joshirishabh1904/BlindNav/CAD/sketches/stick_design/BlindNav_Stick_Sketch.jpeg

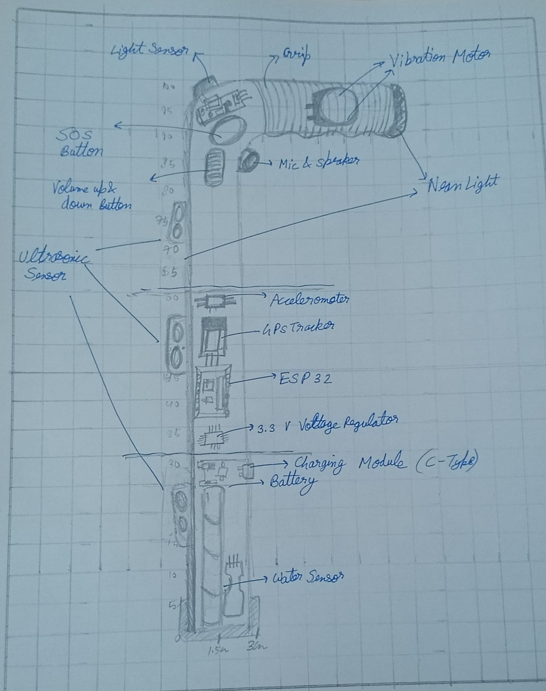
CAD/sketches/stick_design/BlindNav_Stick_Sketch.jpeg
