joshirishabh1904/BlindNav/CAD/sketches/stick_design/BluePrint_of_Stick.jpeg

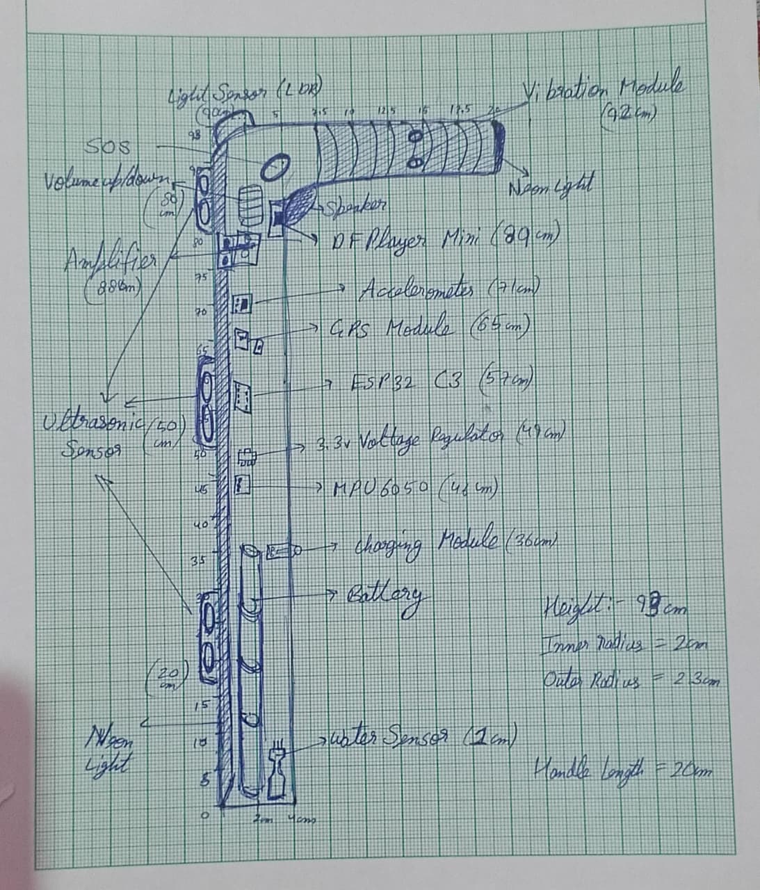
CAD/sketches/stick_design/BluePrint_of_Stick.jpeg
