joshirishabh1904/BlindNav/CAD/3d_model/3d_Stick_Design/Handle.png

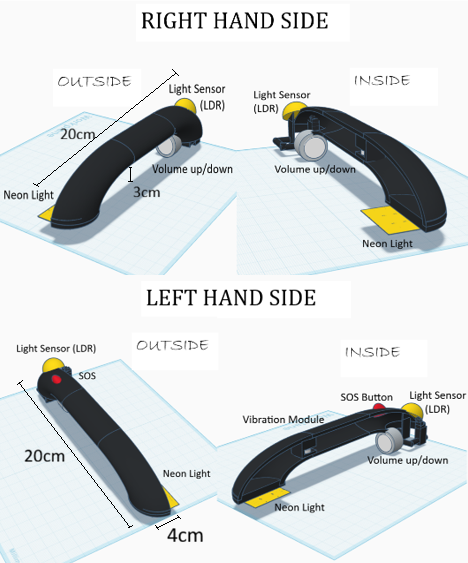
CAD/3d_model/3d_Stick_Design/Handle.png
