joshirishabh1904/BlindNav/CAD/3d_model/3d_Stick_Design/Photos/Front_Side_Stick.png

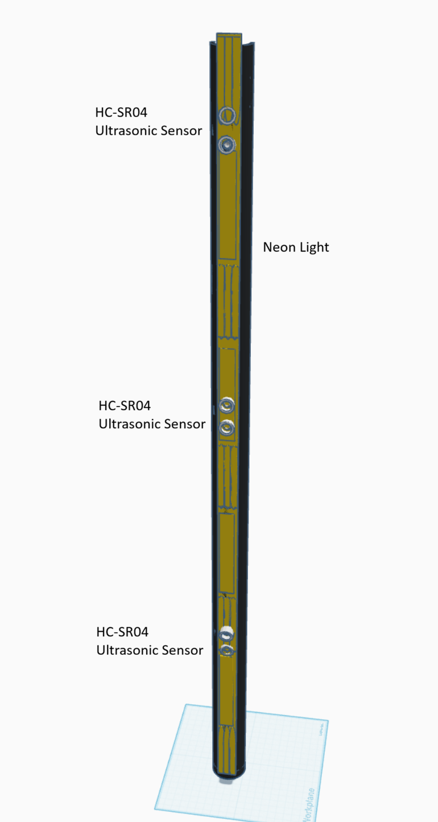
CAD/3d_model/3d_Stick_Design/Photos/Front_Side_Stick.png
