joshirishabh1904/BlindNav/CAD/3d_model/3d_Stick_Design/Photos/Right_Side_Handle.png

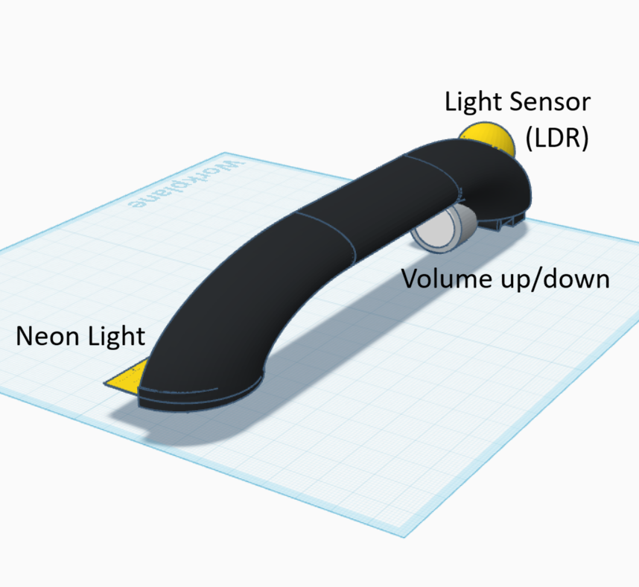
CAD/3d_model/3d_Stick_Design/Photos/Right_Side_Handle.png
