joshirishabh1904/BlindNav/CAD/3d_model/3d_Stick_Design/Photos/Stick_Photo.png

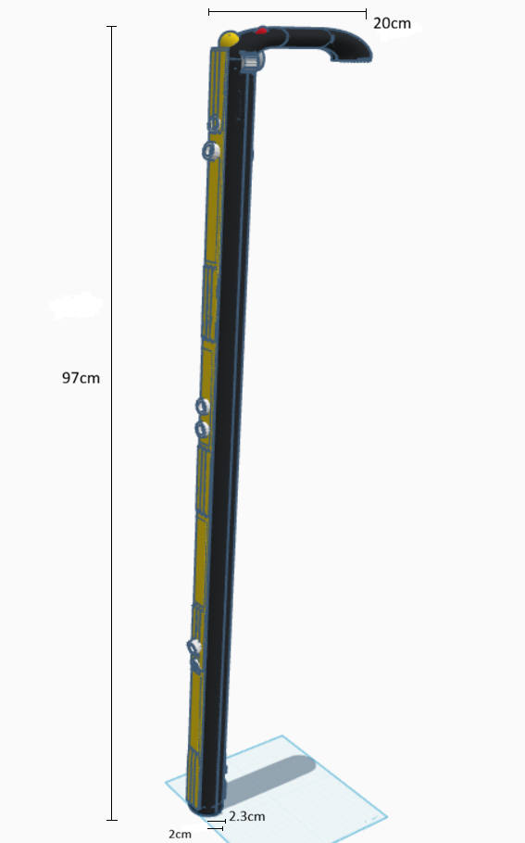
CAD/3d_model/3d_Stick_Design/Photos/Stick_Photo.png
