joshirishabh1904/BlindNav/CAD/3d_model/3d_Stick_Design/Photos/Vibration_Module_Holder.png

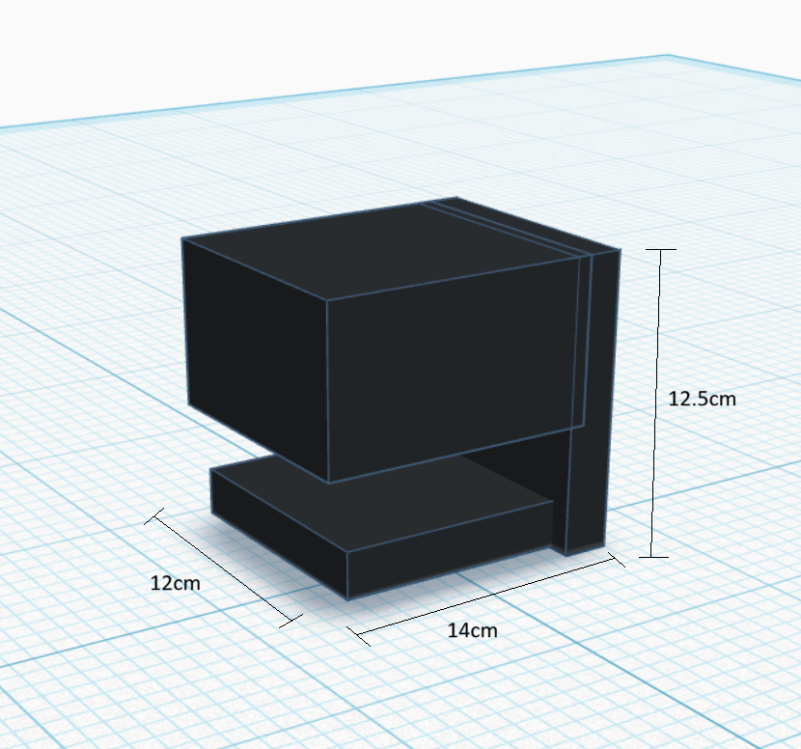
CAD/3d_model/3d_Stick_Design/Photos/Vibration_Module_Holder.png
