joshirishabh1904/BlindNav/Hardware/Schematic_Diagram/BlindNav_SCH_Schematic.png

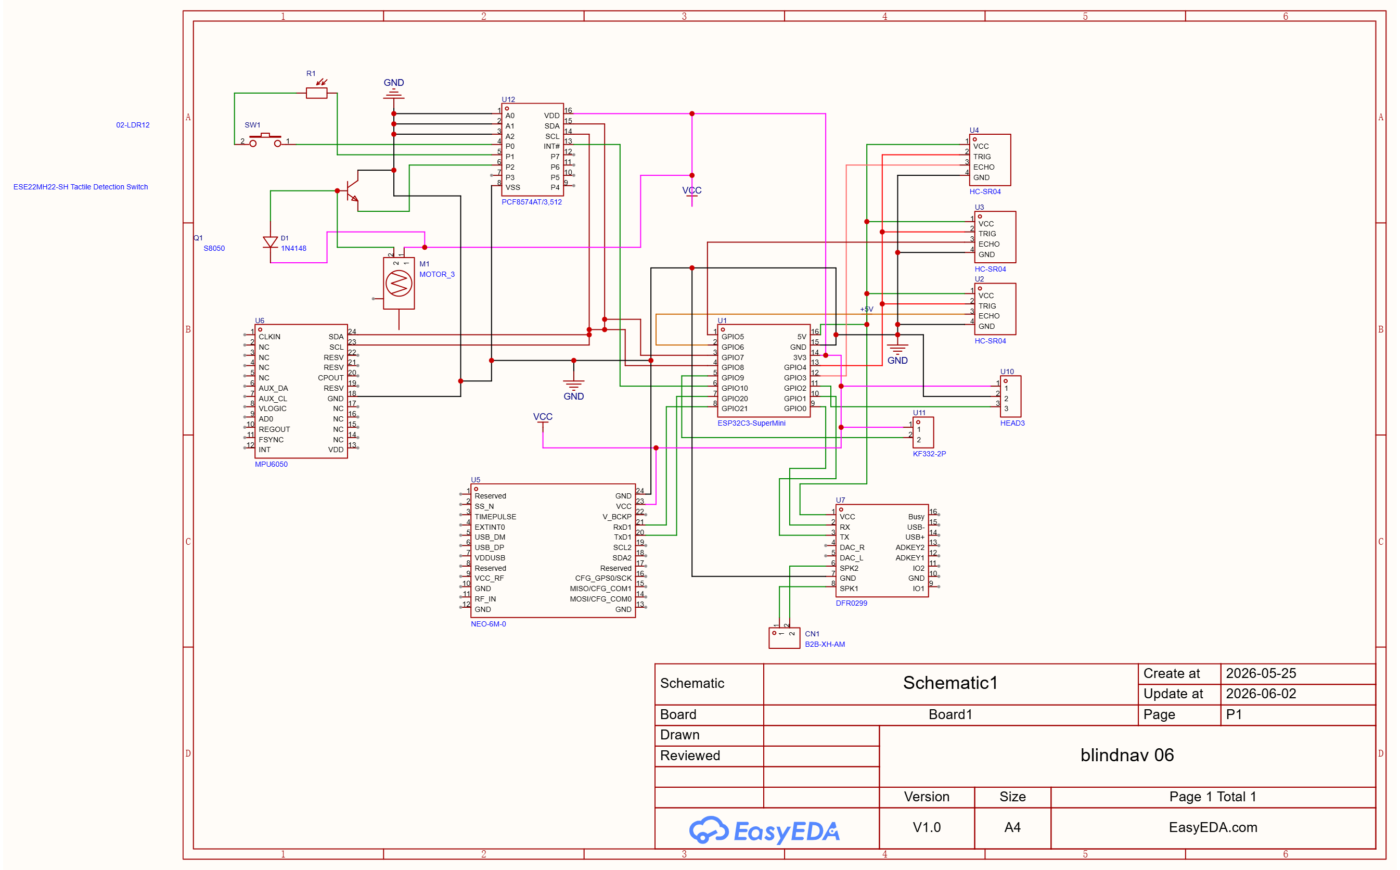
Hardware/Schematic_Diagram/BlindNav_SCH_Schematic.png
