joshirishabh1904/BlindNav/Hardware/Working_Principle/location_output_of_mpu6050.png

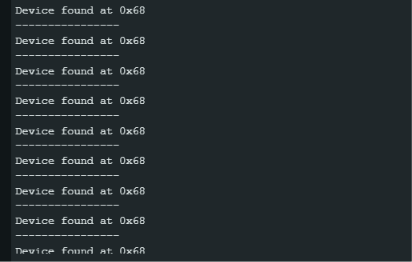
Hardware/Working_Principle/location_output_of_mpu6050.png
