joshirishabh1904/BlindNav/Hardware/Working_Principle/ultrasonic-head-ground-stairs_out.png

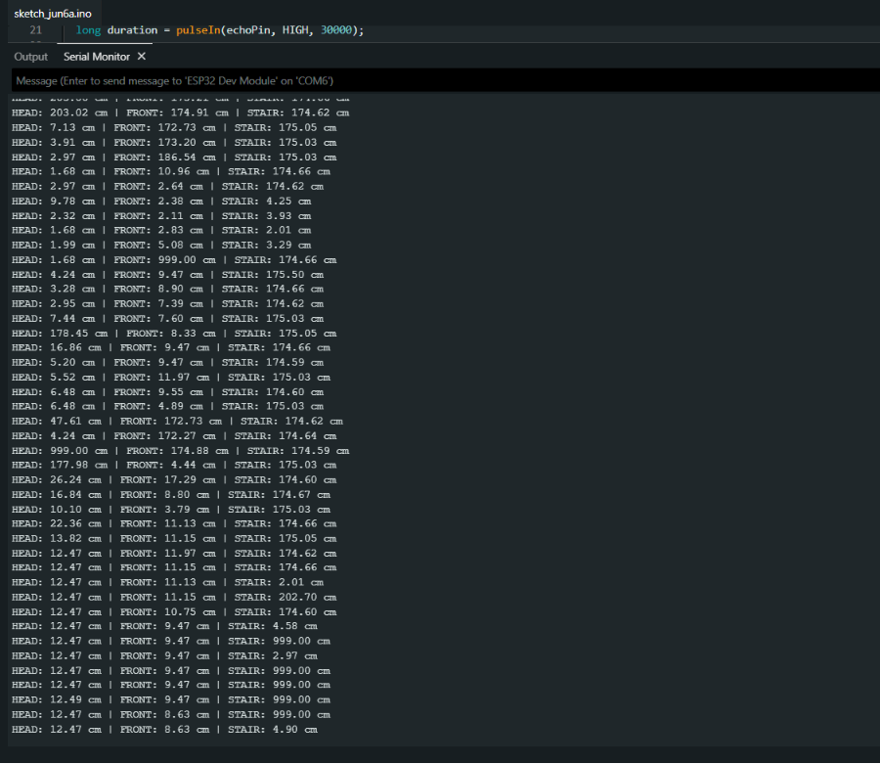
Hardware/Working_Principle/ultrasonic-head-ground-stairs_out.png
