joshirishabh1904/BlindNav/CAD/3d_model/Components/Inside_Component_02.png

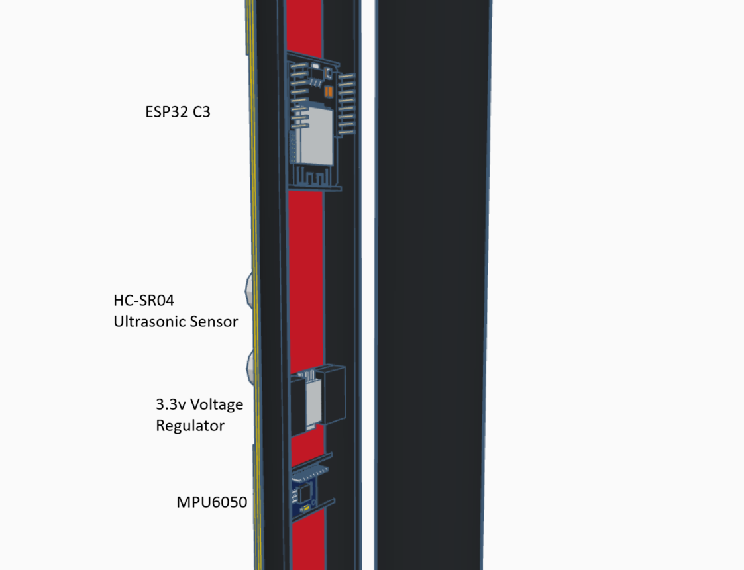
CAD/3d_model/Components/Inside_Component_02.png
