joshirishabh1904/BlindNav/CAD/3d_model/Components/Inside_Component_04.png

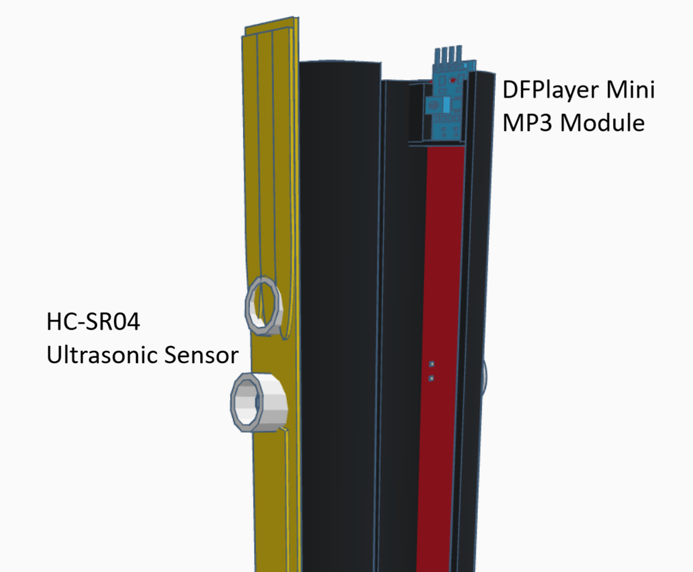
CAD/3d_model/Components/Inside_Component_04.png
