joshirishabh1904/BlindNav/CAD/3d_model/Components/Right_Handle_Inside_Component_01.png

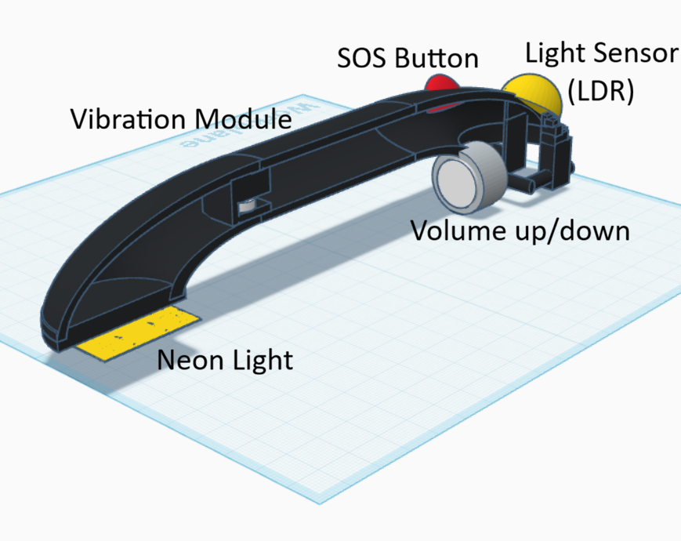
CAD/3d_model/Components/Right_Handle_Inside_Component_01.png
