joshirishabh1904/BlindNav/CAD/sketches/component_sketch/Component_Sketch_01.jpeg

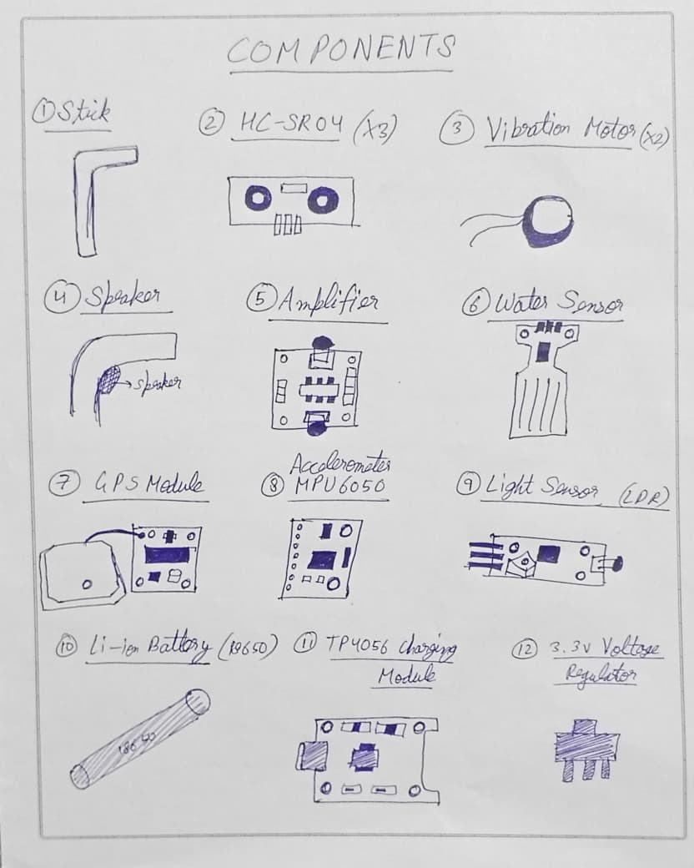
CAD/sketches/component_sketch/Component_Sketch_01.jpeg
