joshirishabh1904/BlindNav/CAD/sketches/component_sketch/Component_Sketch_02.jpeg

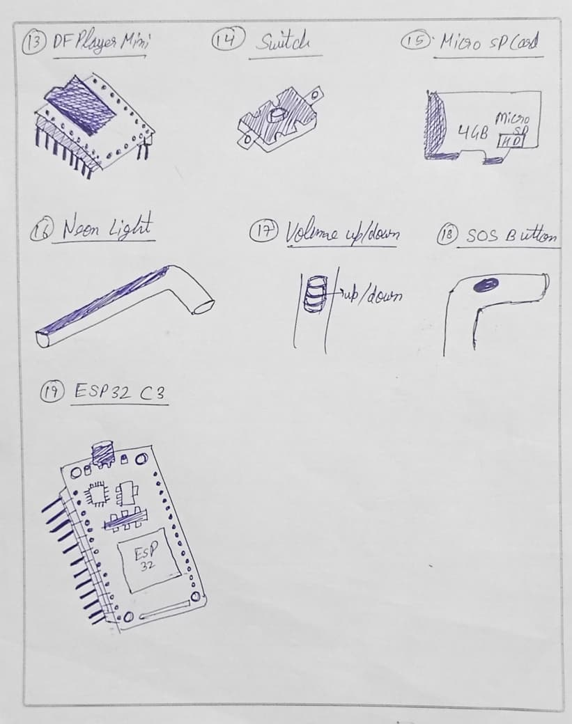
CAD/sketches/component_sketch/Component_Sketch_02.jpeg
