joshirishabh1904/BlindNav/Hardware/Wiring_Diagram.jpeg

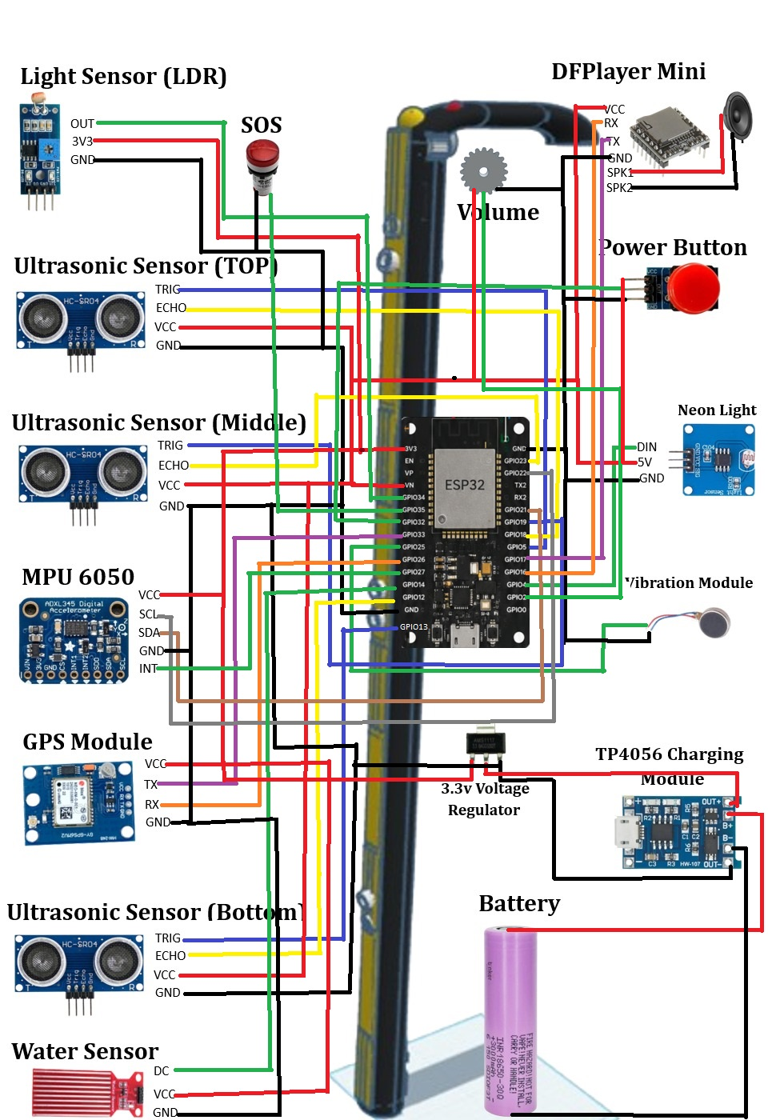
Hardware/Wiring_Diagram.jpeg
